NOVA-Cluster/nova-mini/nova-mini (receiver)/src/Tasks.cpp

#include "Tasks.h"
#include "utilities/Utilities.h"  // Updated path
#include "configuration.h"
#include "main.h"
#include <FastLED.h>
#include "SimonaDisplaySequences.h" // Added include for LED animation functions
// ...other necessary includes...

// TaskWeb definition
void TaskWeb(void *pvParameters)
{
    // ...existing setup code from TaskWeb...
    UBaseType_t uxHighWaterMark;
    TaskHandle_t xTaskHandle = xTaskGetCurrentTaskHandle();
    const char *pcTaskName = pcTaskGetName(xTaskHandle);
    safeSerialPrintf("TaskWeb is running\n");
    while (1)
    {
        webLoop();  // Make sure this line exists
        vTaskDelay(pdMS_TO_TICKS(100)); // Add a small delay to prevent watchdog triggers

        yield();
        delay(1);
        static uint32_t lastExecutionTime = 0;
        if (millis() - lastExecutionTime >= REPORT_TASK_INTERVAL)
        {
            uxHighWaterMark = uxTaskGetStackHighWaterMark(NULL);
            safeSerialPrintf("%s stack free - %d running on core %d\n", pcTaskName, uxHighWaterMark, xPortGetCoreID());
            lastExecutionTime = millis();
        }
    }
}

// TaskOutputs definition
void TaskOutputs(void *pvParameters)
{
    // ...existing code from TaskOutputs...
    UBaseType_t uxHighWaterMark;
    TaskHandle_t xTaskHandle = xTaskGetCurrentTaskHandle();
    const char *pcTaskName = pcTaskGetName(xTaskHandle);
    safeSerialPrintf("TaskOutputs is running\n");
    while (1)
    {
        uint32_t currentTime = millis();
        // ...existing relay control code...
        for (int i = 0; i < NUM_RELAYS; i++)
        {
            if (relayTasks[i].active)
            {
                if (relayTasks[i].longActive)
                {
                    if (currentTime >= relayTasks[i].offTime)
                    {
                        sr.set(i, LOW);
                        relayTasks[i].active = false;
                    }
                }
                else
                {
                    if (currentTime >= relayTasks[i].offTime ||
                        (currentTime - relayTasks[i].startTime) >= MAX_RELAY_DURATION)
                    {
                        sr.set(i, LOW);
                        relayTasks[i].active = false;
                    }
                }
            }
        }
        // ...other existing code...
        yield();
        delay(1);
        static uint32_t lastExecutionTime = 0;
        if (millis() - lastExecutionTime >= REPORT_TASK_INTERVAL)
        {
            uxHighWaterMark = uxTaskGetStackHighWaterMark(NULL);
            safeSerialPrintf("%s stack free - %d running on core %d\n", pcTaskName, uxHighWaterMark, xPortGetCoreID());
            lastExecutionTime = millis();
        }
    }
}

// TaskPulseRelay definition
void TaskPulseRelay(void *pvParameters)
{
    UBaseType_t uxHighWaterMark;
    TaskHandle_t xTaskHandle = xTaskGetCurrentTaskHandle();
    const char *pcTaskName = pcTaskGetName(xTaskHandle);
    safeSerialPrintf("TaskPulseRelay is running\n");
    while (1)
    {
        uint32_t currentTime = millis();
        static uint32_t lastPulse = 0;
        if (currentTime - lastPulse >= 1000)
        {
            triggerRelay(7, 50); // Restored: Pulse relay 7 every second
            lastPulse = currentTime;
        }
        yield();
        delay(1);
        static uint32_t lastExecutionTime = 0;
        if (currentTime - lastExecutionTime >= REPORT_TASK_INTERVAL)
        {
            uxHighWaterMark = uxTaskGetStackHighWaterMark(NULL);
            safeSerialPrintf("%s stack free - %d running on core %d\n", pcTaskName, uxHighWaterMark, xPortGetCoreID());
            lastExecutionTime = currentTime;
        }
    }
}

// TaskFastLED definition
void TaskFastLED(void *pvParameters)
{
    UBaseType_t uxHighWaterMark;
    TaskHandle_t xTaskHandle = xTaskGetCurrentTaskHandle();
    const char *pcTaskName = pcTaskGetName(xTaskHandle);
    safeSerialPrintf("TaskFastLED is running\n");
    
    uint32_t lastExecutionTime = 0; // new watermark timer
    for (;;) {
        switch (currentLEDAnimationState) {
            case LED_WAITING:
                displaySimonaStageWaitingAnimation();
                break;
            case LED_SEQUENCE_GENERATION:
                displaySimonaStageSequenceGenerationAnimation();
                break;
            case LED_TRANSITION:
                displaySimonaStageTransitionAnimation();
                break;
            case LED_INPUT_COLLECTION:
                displaySimonaStageInputCollectionAnimation();
                break;
            case LED_VERIFICATION:
                displaySimonaStageVerificationAnimation();
                break;
            case LED_GAME_LOST:
                displaySimonaStageGameLostAnimation();
                break;
            case LED_GAME_WIN:
                displaySimonaStageGameWinAnimation();
                break;
            case LED_RESET:
                displaySimonaStageResetAnimation();
                break;
            case LED_ROUND_TRANSITION:
                displaySimonaStageRoundTransitionAnimation();
                break;
            default:
                // ...existing default code...
                break;
        }
        if (millis() - lastExecutionTime >= REPORT_TASK_INTERVAL) {
            uxHighWaterMark = uxTaskGetStackHighWaterMark(NULL);
            safeSerialPrintf("%s stack free - %d running on core %d\n", pcTaskName, uxHighWaterMark, xPortGetCoreID());
            lastExecutionTime = millis();
        }
        vTaskDelay(10 / portTICK_PERIOD_MS);
    }
}
