NOVA-Cluster/nova-mini/nova-mini (receiver)/src/Tasks.h

#ifndef TASKS_H
#define TASKS_H

#include <Arduino.h>
#include "Web.h"  // Add this include

void TaskWeb(void *pvParameters);
void TaskOutputs(void *pvParameters);
void TaskPulseRelay(void *pvParameters);
void TaskFastLED(void *pvParameters);

#endif // TASKS_H
