NOVA-Cluster/nova-mini/nova-mini (receiver)/src/utilities/Utilities.h

#ifndef UTILITIES_H
#define UTILITIES_H

#include <Arduino.h>

void initSafeSerial();
void safeSerialPrintf(const char* format, ...);
void NovaLogo();
String getLastFourOfMac();

#endif // UTILITIES_H
