NOVA-Cluster/nova-mini/nova-mini (receiver)/src/SimonaDisplay.h

#ifndef SIMONA_H
#define SIMONA_H

#include "SimonaMessage.h"  // Ensure SimonaMessage is declared

// Declare functions to indicate each stage.
void displaySimonaStageWaiting(const SimonaMessage &msg);
void displaySimonaStageSequenceGeneration(const SimonaMessage &msg);
void displaySimonaStageTransition(const SimonaMessage &msg);
void displaySimonaStageInputCollection(const SimonaMessage &msg);
void displaySimonaStageVerification(const SimonaMessage &msg);
void displaySimonaStageGameLost(const SimonaMessage &msg);
void displaySimonaStageGameWin(const SimonaMessage &msg);
void displaySimonaStageReset(const SimonaMessage &msg);
void displaySimonaStageRoundTransition(const SimonaMessage &msg); // Added for round transition

#endif // SIMONA_H
