NOVA-Cluster/nova-mini/nova-mini (receiver)/src/SimonaDisplaySequences.h

#ifndef SIMONADISPLAYSEQUENCES_H
#define SIMONADISPLAYSEQUENCES_H

// Declare animation functions for new LED states.
void displaySimonaStageSequenceGenerationAnimation();
void displaySimonaStageTransitionAnimation();
void displaySimonaStageInputCollectionAnimation();
void displaySimonaStageVerificationAnimation();
void displaySimonaStageGameLostAnimation();
void displaySimonaStageGameWinAnimation();
void displaySimonaStageResetAnimation();
void displaySimonaStageWaitingAnimation();
void displaySimonaStageRoundTransitionAnimation(); // Added for round transition

#endif // SIMONADISPLAYSEQUENCES_H
